petervojtek/stalker/images/02.jpg

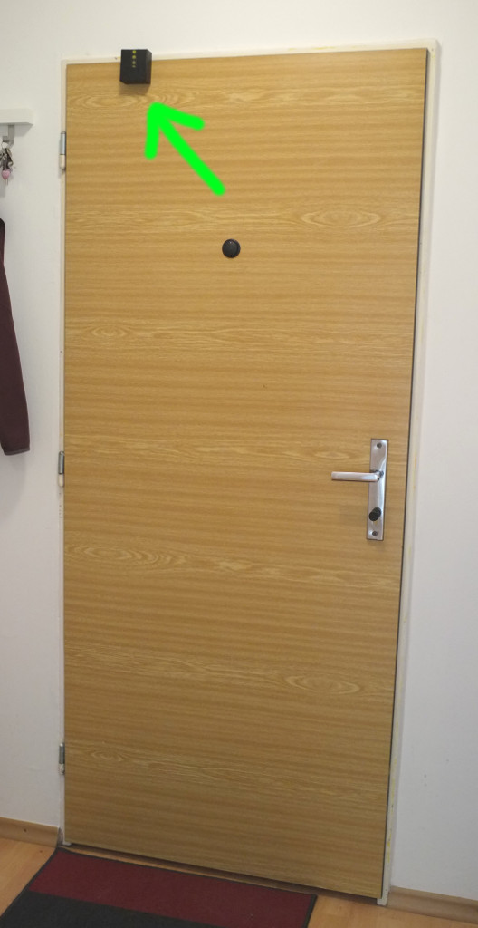
images/02.jpg
